NotARoomba/Linea/assets/linea.jpg

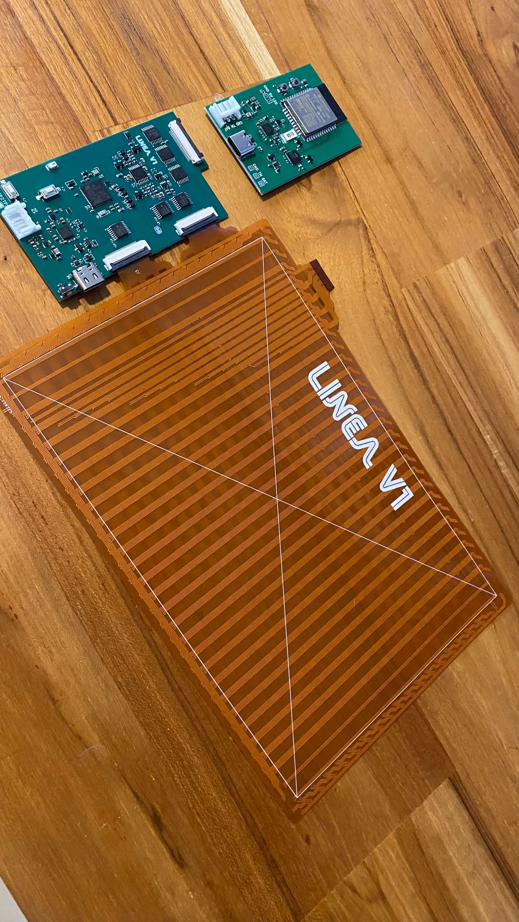
assets/linea.jpg
